greed42/Mini_Drawers_Ultimate/images/0a24cfd5650f65f2fee0652f7383d565_preview_featured.jpg

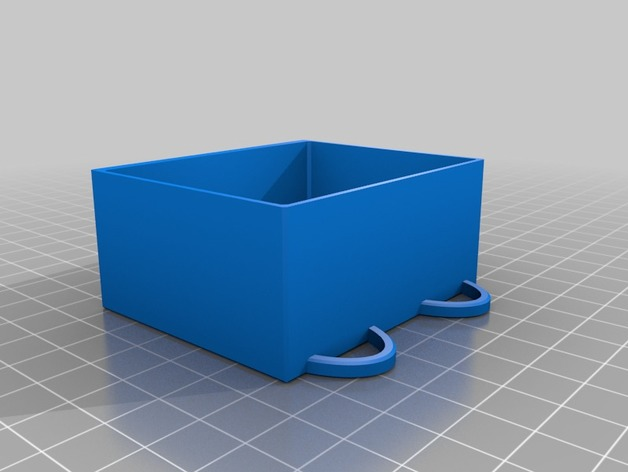
images/0a24cfd5650f65f2fee0652f7383d565_preview_featured.jpg
