greed42/Mini_Drawers_Ultimate/images/0a53dd162b8f72155c7e9e90befe79cb_preview_featured.jpg

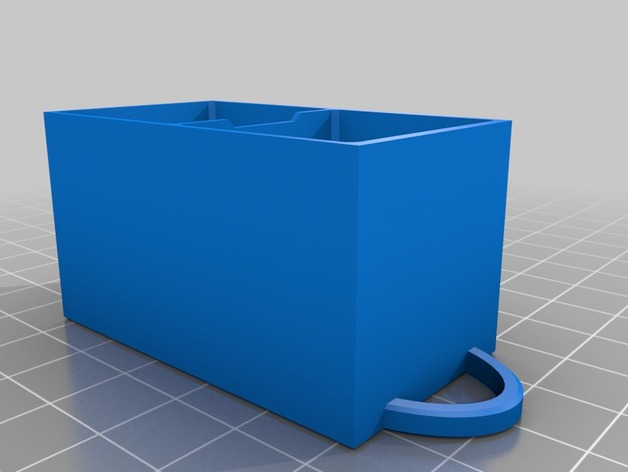
images/0a53dd162b8f72155c7e9e90befe79cb_preview_featured.jpg
