greed42/Mini_Drawers_Ultimate/images/0ca46b2de7a758f1d5402f7cd417421c_preview_featured.jpg

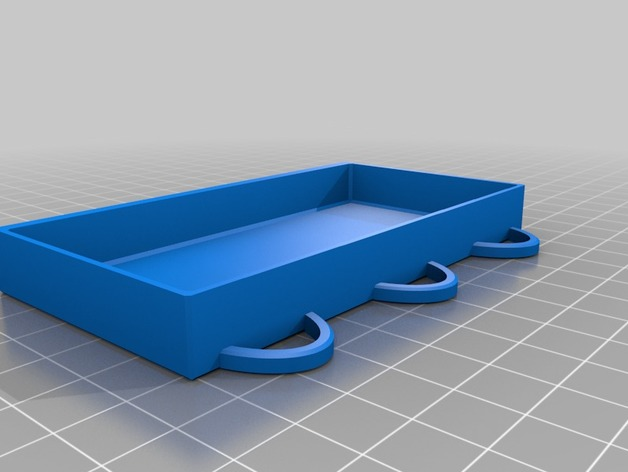
images/0ca46b2de7a758f1d5402f7cd417421c_preview_featured.jpg
