greed42/Mini_Drawers_Ultimate/images/1c9a940551aba49c20e5ade4921b8e68_preview_featured.jpg

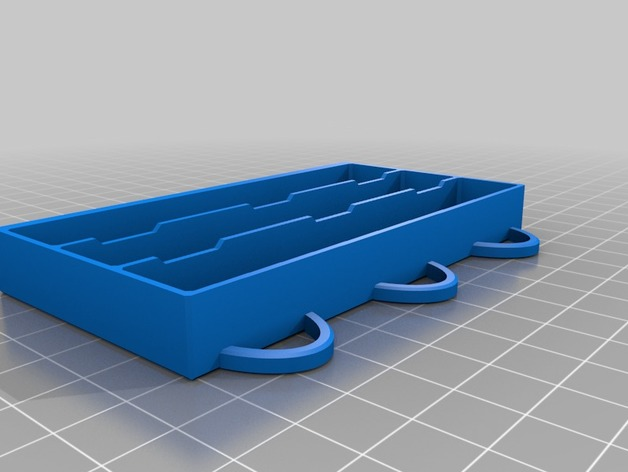
images/1c9a940551aba49c20e5ade4921b8e68_preview_featured.jpg
