greed42/Mini_Drawers_Ultimate/images/2fe49b50781997d6599957611f890632_preview_featured.jpg

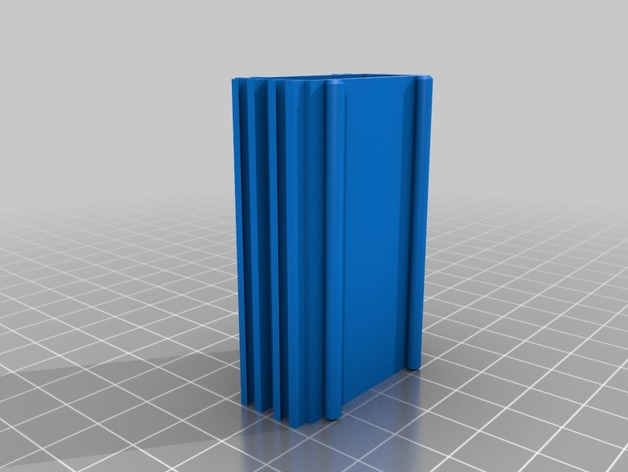
images/2fe49b50781997d6599957611f890632_preview_featured.jpg
