greed42/Mini_Drawers_Ultimate/images/4c2f461d4b738c59763611d66d30dad5_preview_featured.jpg

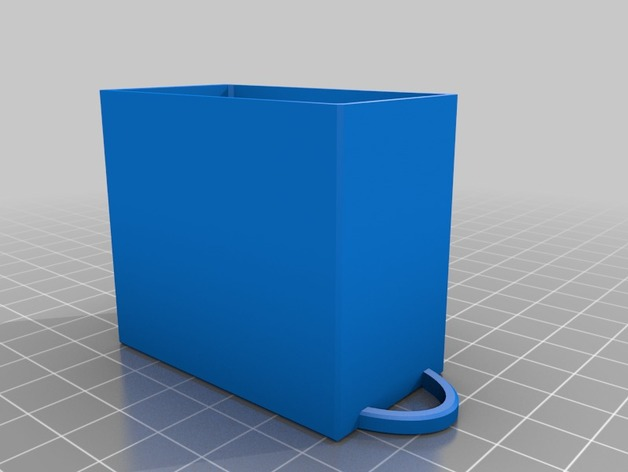
images/4c2f461d4b738c59763611d66d30dad5_preview_featured.jpg
