greed42/Mini_Drawers_Ultimate/images/4ddb12a624d50258dd31a015ba16a962_preview_featured.jpg

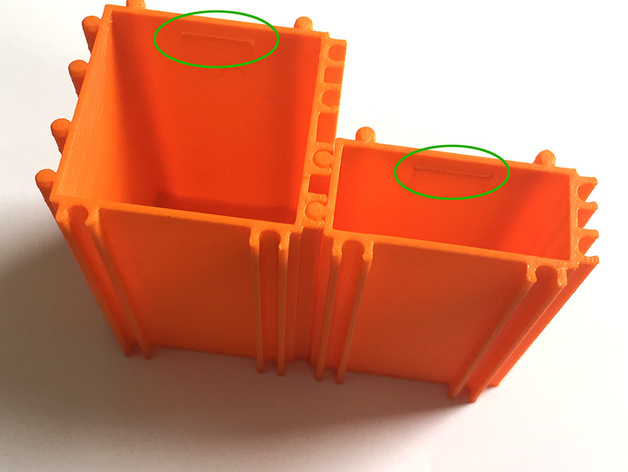
images/4ddb12a624d50258dd31a015ba16a962_preview_featured.jpg
