greed42/Mini_Drawers_Ultimate/images/5e9b697154c2deef4179bea128791556_preview_featured.jpg

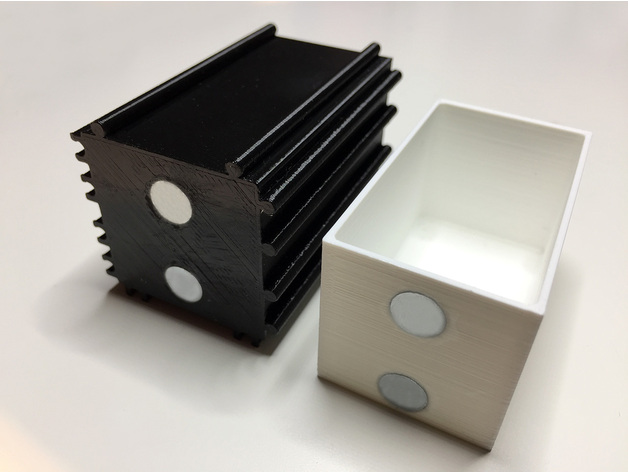
images/5e9b697154c2deef4179bea128791556_preview_featured.jpg
