greed42/Mini_Drawers_Ultimate/images/6dbaf6c8708ecae2bc6790827a99efa1_preview_featured.jpg

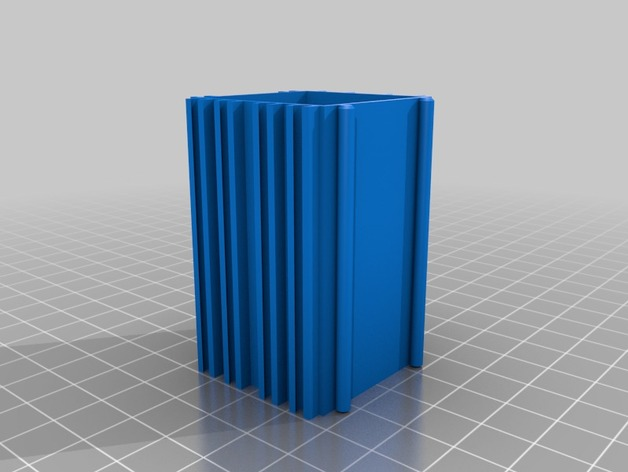
images/6dbaf6c8708ecae2bc6790827a99efa1_preview_featured.jpg
