greed42/Mini_Drawers_Ultimate/images/7b8f287952d526c621f49c0cf82e3b4b_preview_featured.jpg

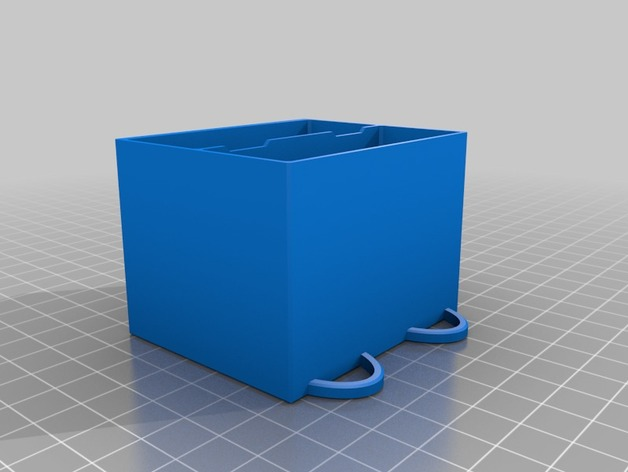
images/7b8f287952d526c621f49c0cf82e3b4b_preview_featured.jpg
