greed42/Mini_Drawers_Ultimate/images/7f0093e2a322c83190b559ce54492e52_preview_featured.jpg

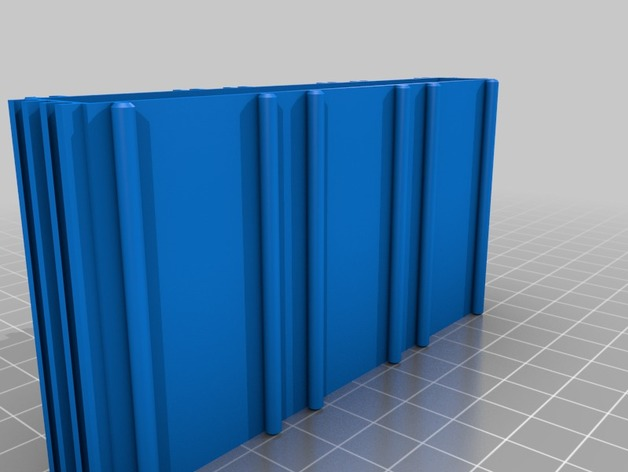
images/7f0093e2a322c83190b559ce54492e52_preview_featured.jpg
