greed42/Mini_Drawers_Ultimate/images/7fe03153f6410948815649d941ac0b7e_preview_featured.jpg

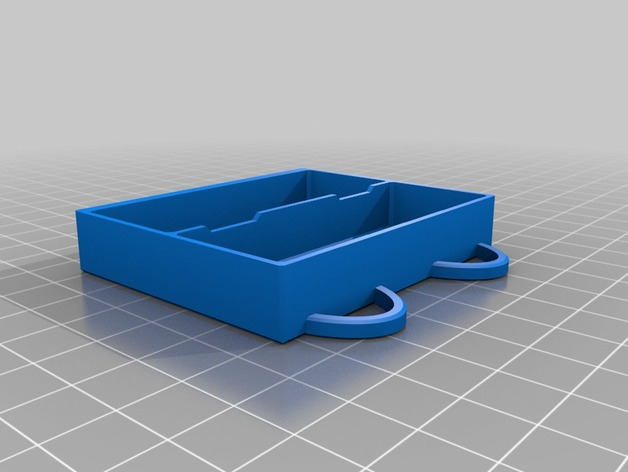
images/7fe03153f6410948815649d941ac0b7e_preview_featured.jpg
