greed42/Mini_Drawers_Ultimate/images/32acb8aaa7054c7361c1b5d2ec2757fa_preview_featured.jpg

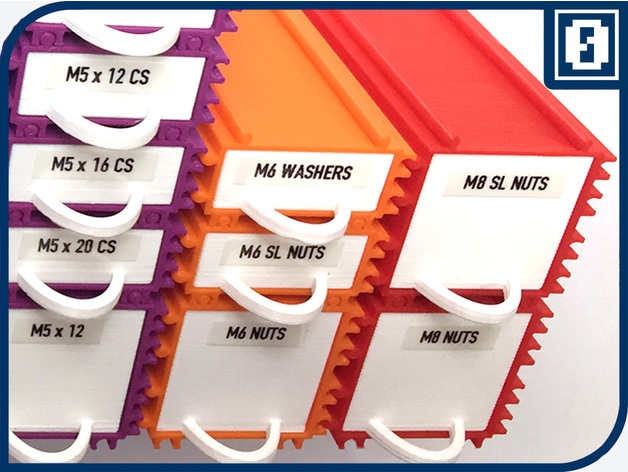
images/32acb8aaa7054c7361c1b5d2ec2757fa_preview_featured.jpg
