greed42/Mini_Drawers_Ultimate/images/32dee0f93447d803b35d06009c72c7d5_preview_featured.jpg

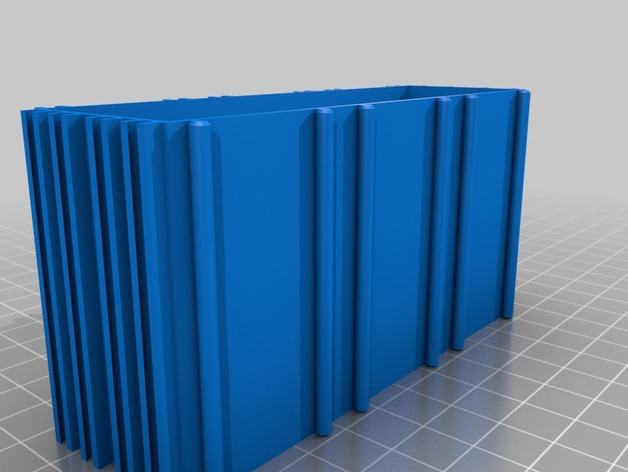
images/32dee0f93447d803b35d06009c72c7d5_preview_featured.jpg
