greed42/Mini_Drawers_Ultimate/images/46a52b9ae08081f0f0b2e6e8d7b132d8_preview_featured.jpg

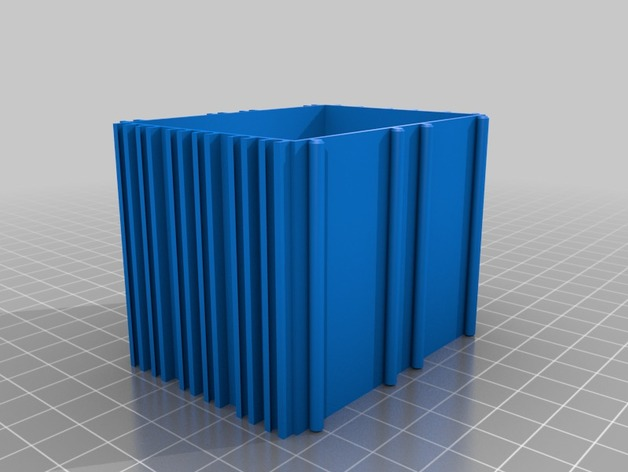
images/46a52b9ae08081f0f0b2e6e8d7b132d8_preview_featured.jpg
