greed42/Mini_Drawers_Ultimate/images/71ca9c4c97bb1e561b7ab4358689eb5e_preview_featured.jpg

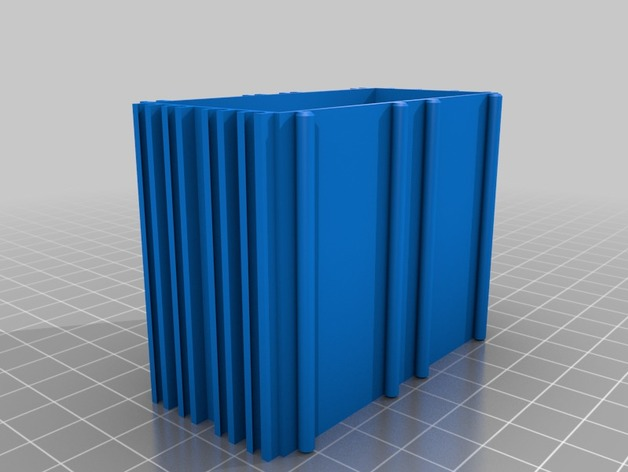
images/71ca9c4c97bb1e561b7ab4358689eb5e_preview_featured.jpg
