greed42/Mini_Drawers_Ultimate/images/408dd901ebeae069e11c7ea489d1516e_preview_featured.jpg

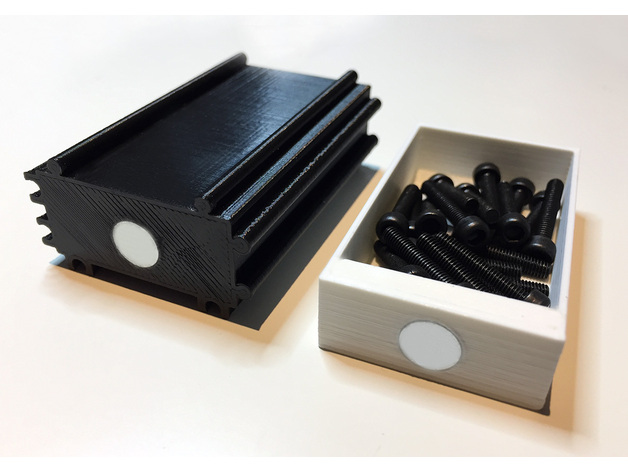
images/408dd901ebeae069e11c7ea489d1516e_preview_featured.jpg
