greed42/Mini_Drawers_Ultimate/images/852ab4ac9241c05d7ac25c2f6cb6ef0e_preview_featured.jpg

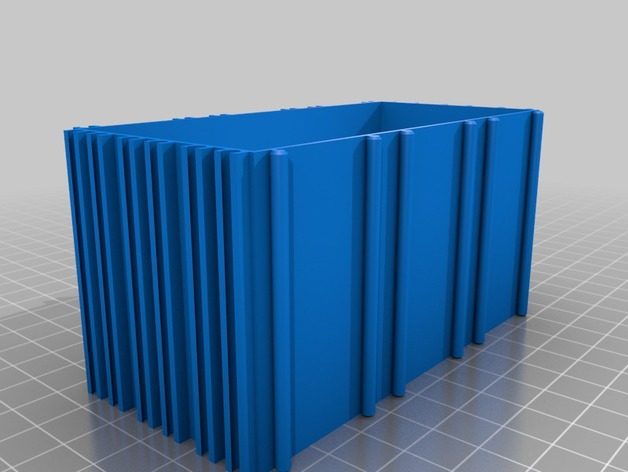
images/852ab4ac9241c05d7ac25c2f6cb6ef0e_preview_featured.jpg
