greed42/Mini_Drawers_Ultimate/images/64127c74380bcbb5a7397c8df0195909_preview_featured.jpg

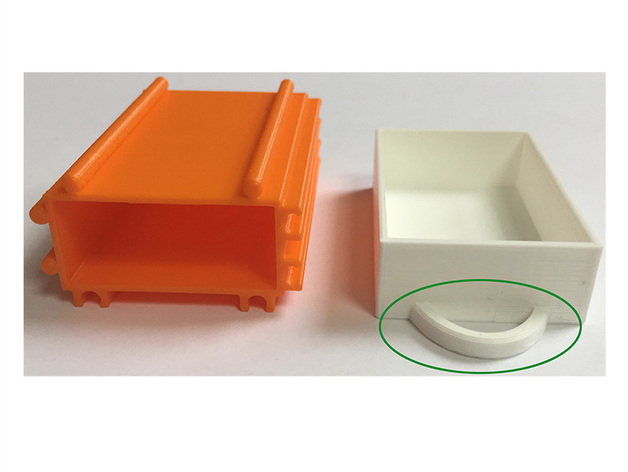
images/64127c74380bcbb5a7397c8df0195909_preview_featured.jpg
