greed42/Mini_Drawers_Ultimate/images/a5263657c8ac7417cfba7f5ac3cf7af2_preview_featured.jpg

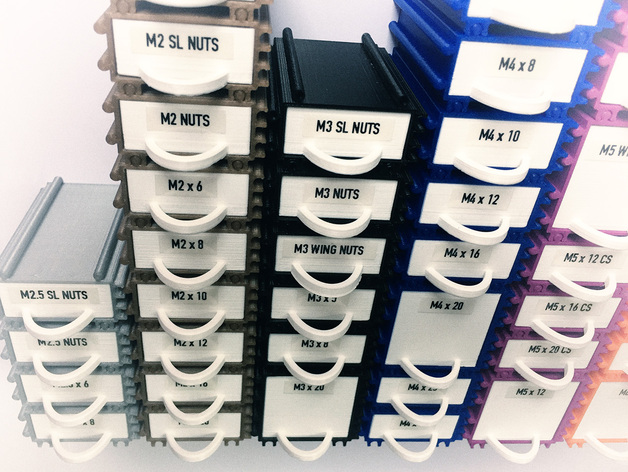
images/a5263657c8ac7417cfba7f5ac3cf7af2_preview_featured.jpg
