greed42/Mini_Drawers_Ultimate/images/c88d1c1aad7d767cea963d23f5f8f326_preview_featured.jpg

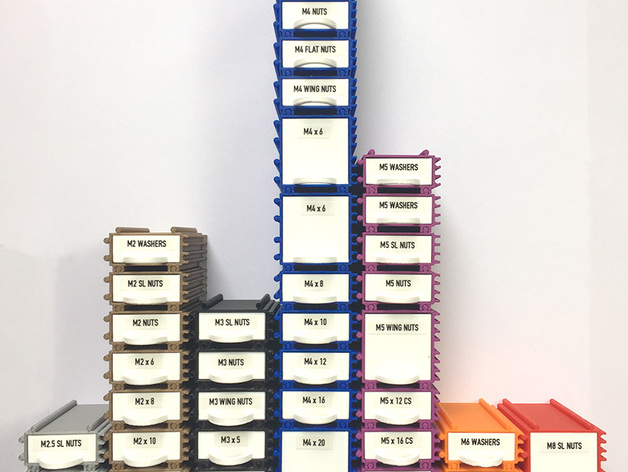
images/c88d1c1aad7d767cea963d23f5f8f326_preview_featured.jpg
