greed42/Mini_Drawers_Ultimate/images/f5fea6e71f09a3ffe9e83b5db6158fe8_preview_featured.JPG

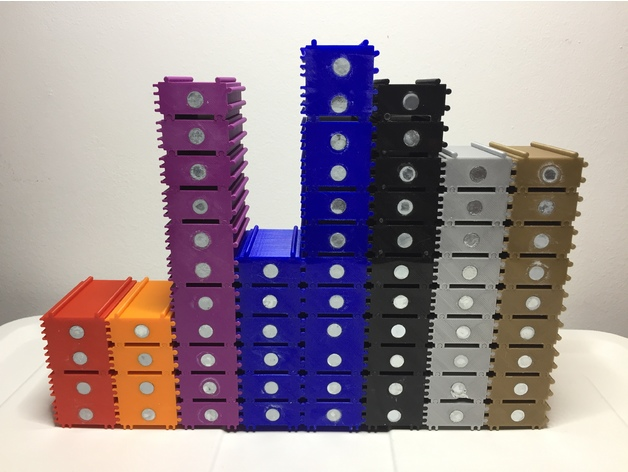
images/f5fea6e71f09a3ffe9e83b5db6158fe8_preview_featured.JPG
