greed42/Mini_Drawers_Ultimate/files/1x1_Drawer_magnet.stl

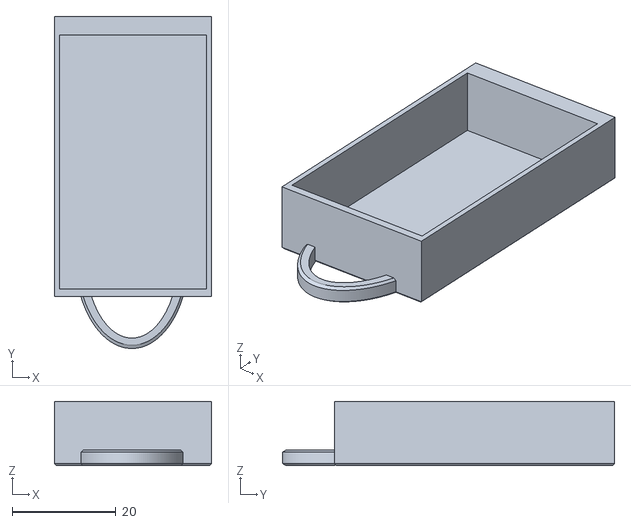
[picture p41: CAD file, 2020-08-03]
files/1x1_Drawer_magnet.stl
30.4 x 64.1 x 12.4
