greed42/Mini_Drawers_Ultimate/files/3x2_House_magnet.stl

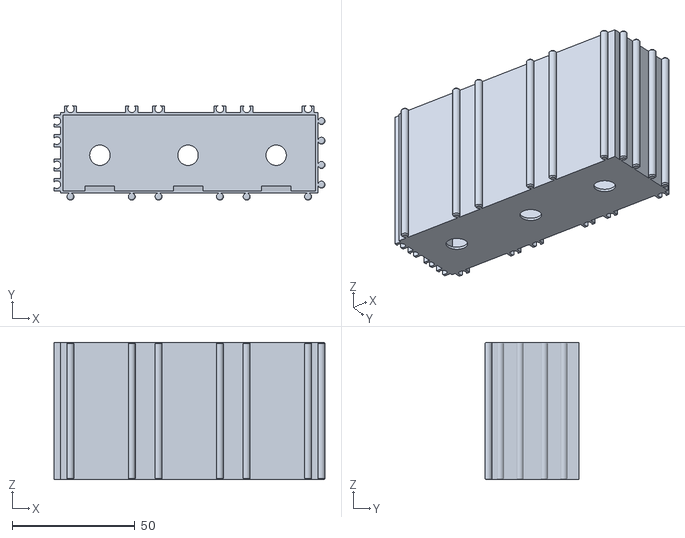
[picture p42: CAD file, 2020-08-03]
files/3x2_House_magnet.stl
110.4 x 38.4 x 56.0
