greed42/Mini_Drawers_Ultimate/files/3x1_Drawer_-_three_slots_magnet.stl

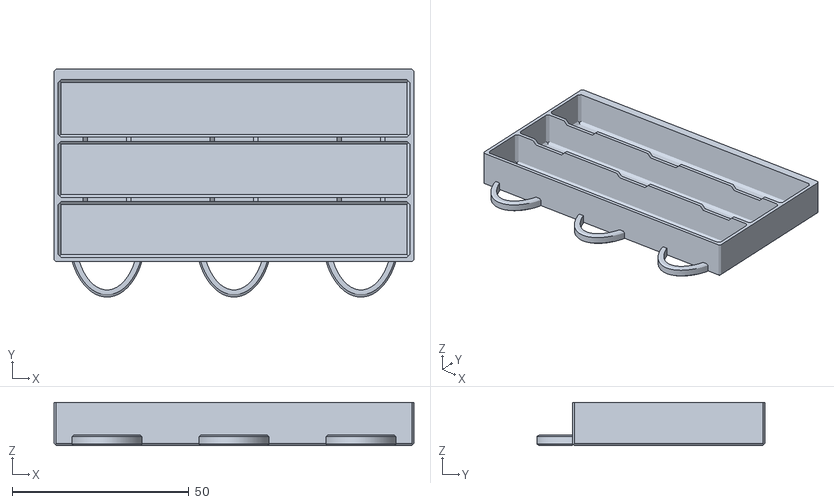
[picture p45: CAD file, 2020-08-03]
files/3x1_Drawer_-_three_slots_magnet.stl
101.8 x 64.5 x 12.2
