greed42/Mini_Drawers_Ultimate/files/1x3_House_magnet.stl

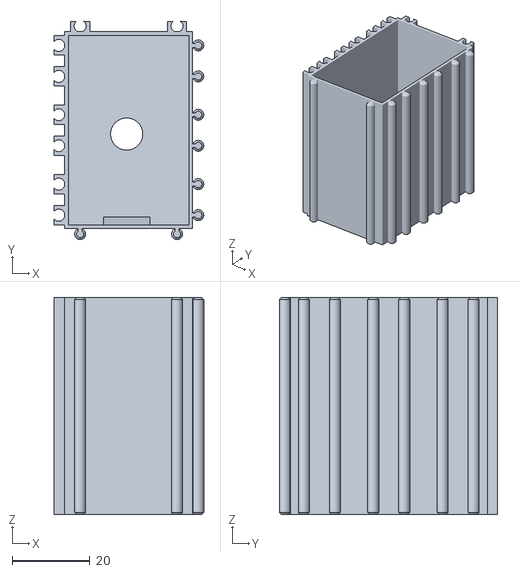
[picture p46: CAD file, 2020-08-03]
files/1x3_House_magnet.stl
38.6 x 56.3 x 56.0
