greed42/Mini_Drawers_Ultimate/files/2x2_House_magnet.stl

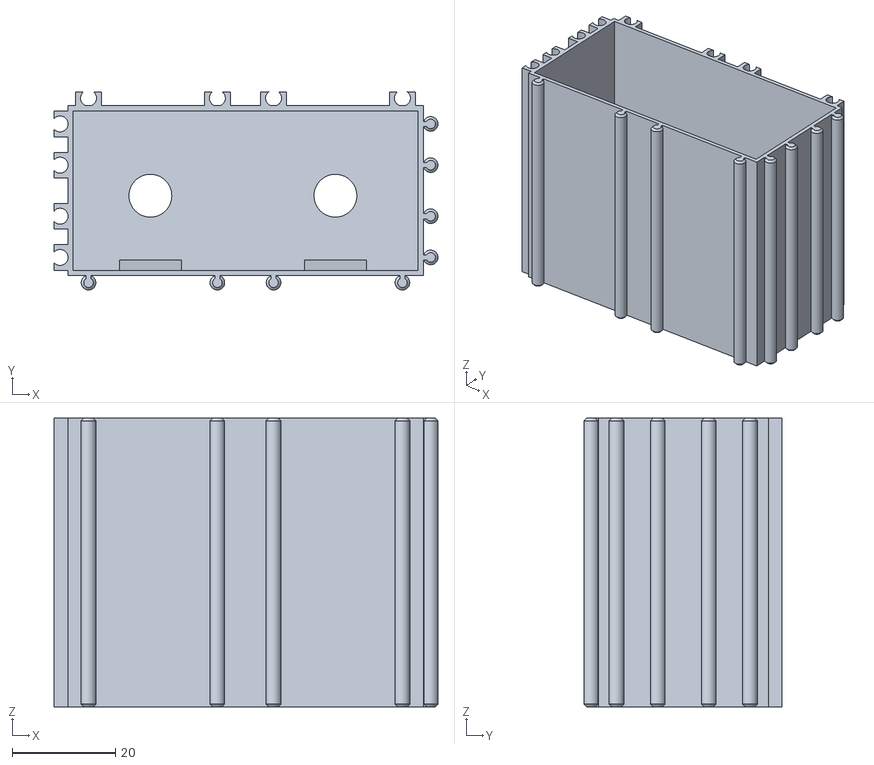
[picture p48: CAD file, 2020-08-03]
files/2x2_House_magnet.stl
74.5 x 38.4 x 56.0
