greed42/Mini_Drawers_Ultimate/files/2x1_Drawer_-_three_slots_magnet.stl

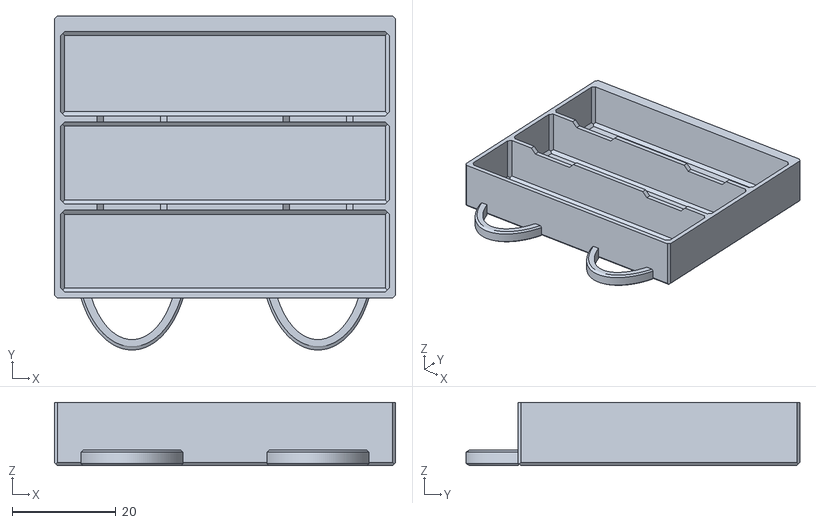
[picture p49: CAD file, 2020-08-03]
files/2x1_Drawer_-_three_slots_magnet.stl
65.9 x 64.5 x 12.2
