greed42/Mini_Drawers_Ultimate/files/3x3_Drawer_-_two_slots_magnet.stl

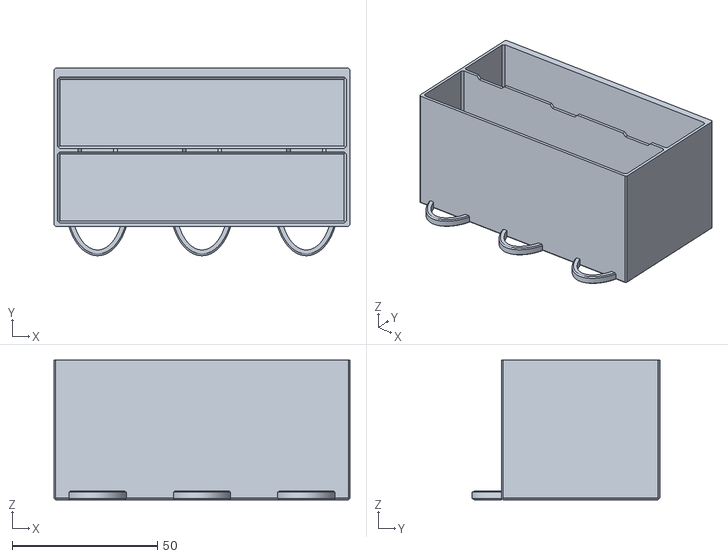
[picture p51: CAD file, 2020-08-03]
files/3x3_Drawer_-_two_slots_magnet.stl
101.8 x 64.5 x 48.0
