greed42/Mini_Drawers_Ultimate/files/3x1_House.stl

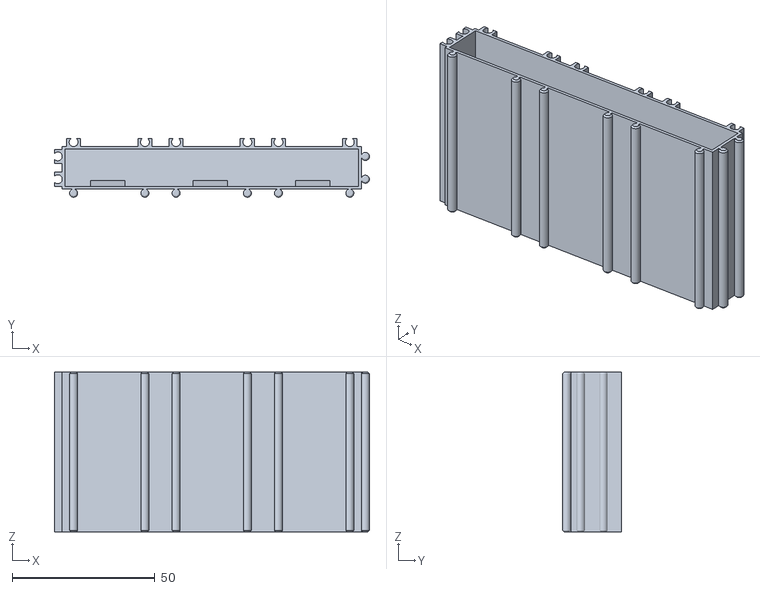
[picture p52: CAD file, 2020-08-03]
files/3x1_House.stl
110.4 x 20.5 x 56.0
