greed42/Mini_Drawers_Ultimate/files/1x1_Drawer_-_two_slots.stl

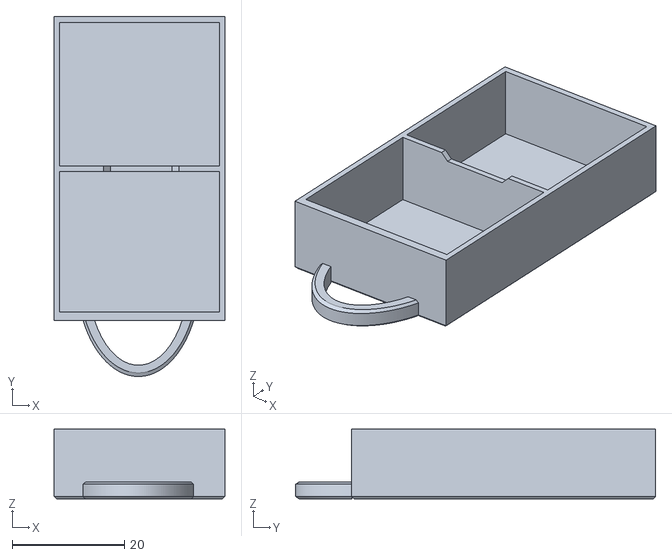
[picture p53: CAD file, 2020-08-03]
files/1x1_Drawer_-_two_slots.stl
30.4 x 64.1 x 12.4
