greed42/Mini_Drawers_Ultimate/files/1x2_House.stl

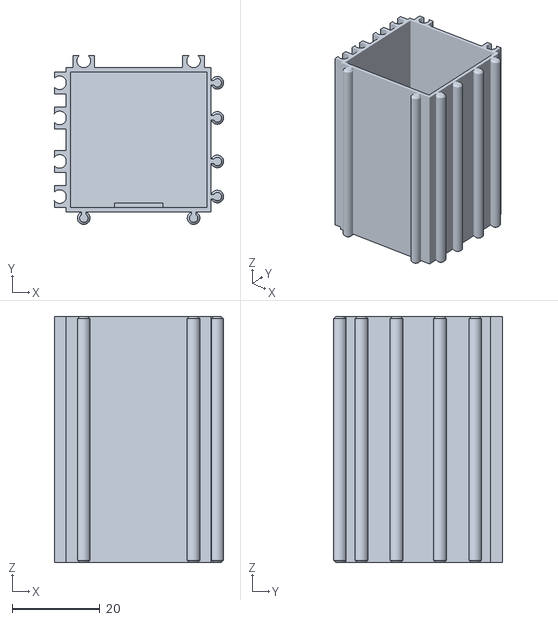
[picture p55: CAD file, 2020-08-03]
files/1x2_House.stl
38.6 x 38.4 x 56.0
