greed42/Mini_Drawers_Ultimate/files/1x2_House_magnet.stl

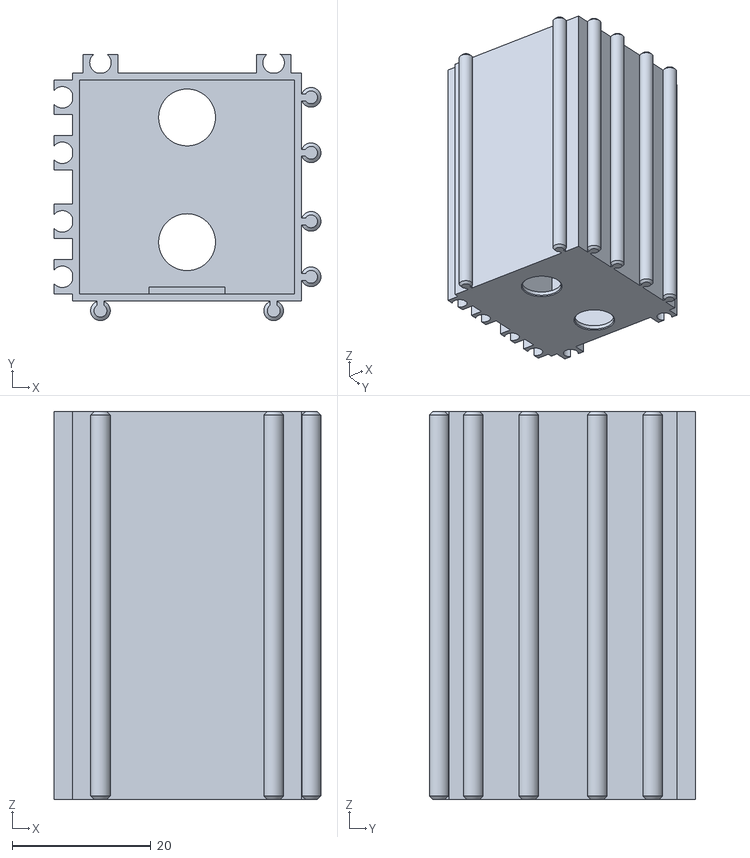
[picture p59: CAD file, 2020-08-03]
files/1x2_House_magnet.stl
38.5 x 38.4 x 56.0
