greed42/Mini_Drawers_Ultimate/files/2x1_Drawer_magnet.stl

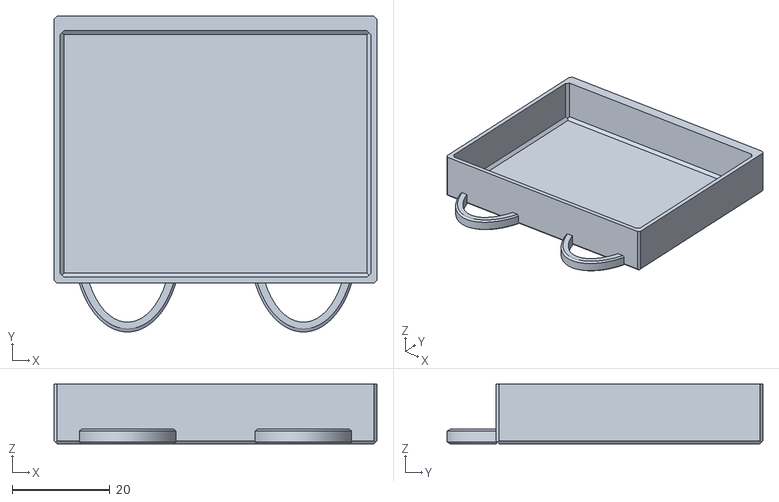
[picture p60: CAD file, 2020-08-03]
files/2x1_Drawer_magnet.stl
65.9 x 64.5 x 12.2
