greed42/Mini_Drawers_Ultimate/files/1x3_Drawer_-_two_slots_magnet.stl

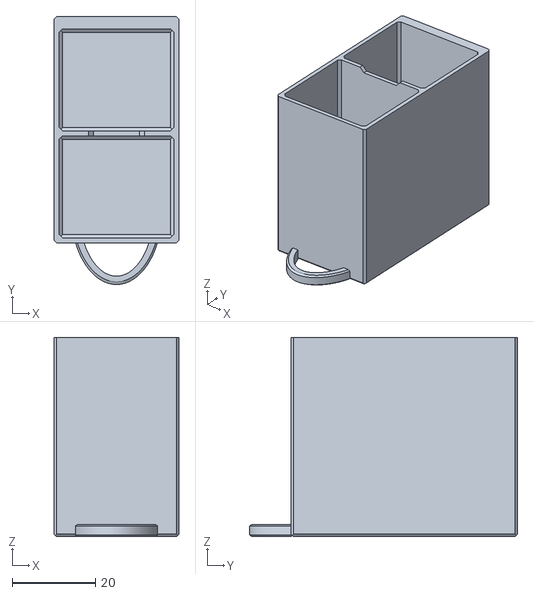
[picture p61: CAD file, 2020-08-03]
files/1x3_Drawer_-_two_slots_magnet.stl
30.0 x 64.5 x 48.0
