greed42/Mini_Drawers_Ultimate/files/1x1_House_magnet.stl

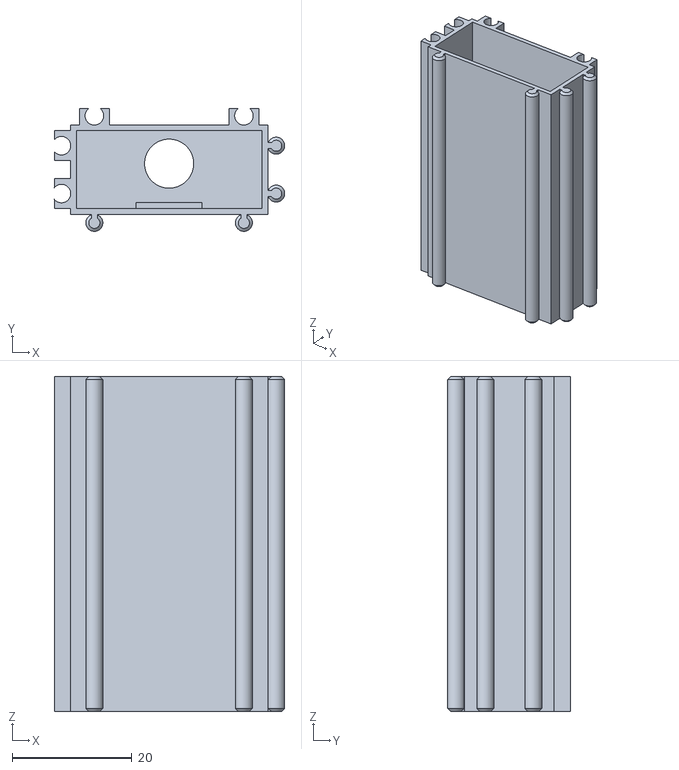
[picture p62: CAD file, 2020-08-03]
files/1x1_House_magnet.stl
38.5 x 20.5 x 56.0
