greed42/Mini_Drawers_Ultimate/files/3x1_House_magnet.stl

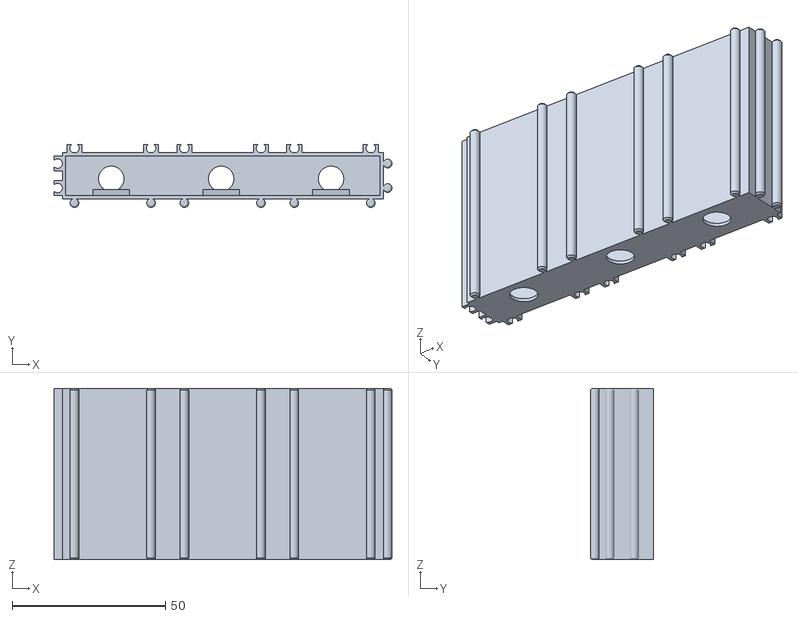
[picture p63: CAD file, 2020-08-03]
files/3x1_House_magnet.stl
110.4 x 20.5 x 56.0
