greed42/Mini_Drawers_Ultimate/files/1x2_Drawer.stl

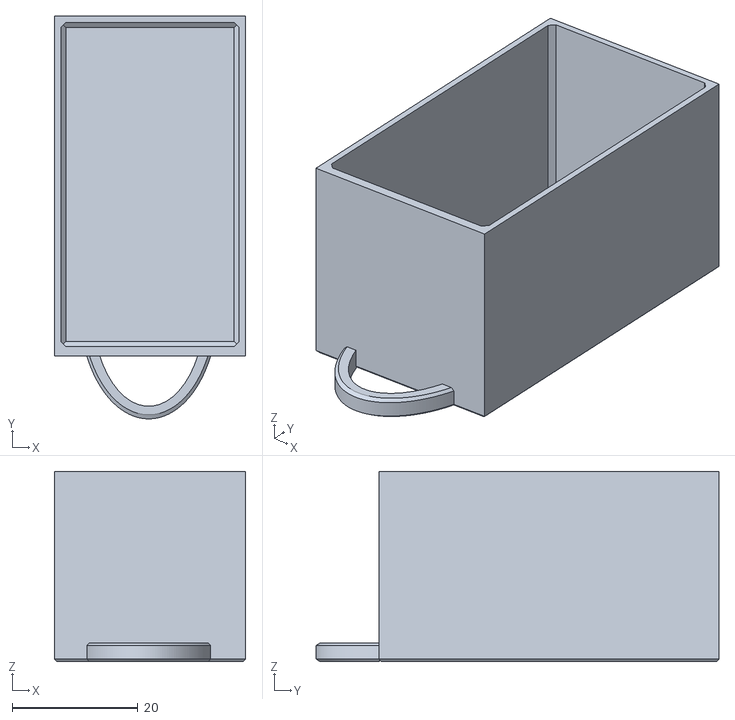
[picture p65: CAD file, 2020-08-03]
files/1x2_Drawer.stl
30.4 x 64.1 x 30.3
