greed42/Mini_Drawers_Ultimate/files/3x3_Drawer_-_three_slots.stl

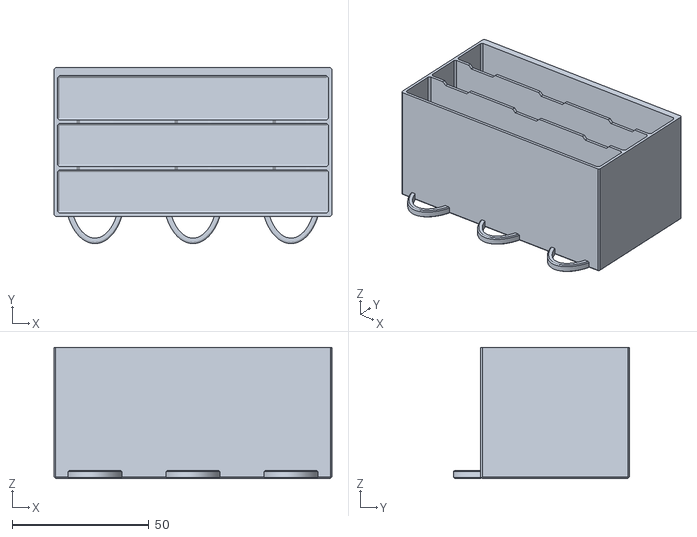
[picture p66: CAD file, 2020-08-03]
files/3x3_Drawer_-_three_slots.stl
101.8 x 64.5 x 48.0
