greed42/Mini_Drawers_Ultimate/files/2x3_House_magnet.stl

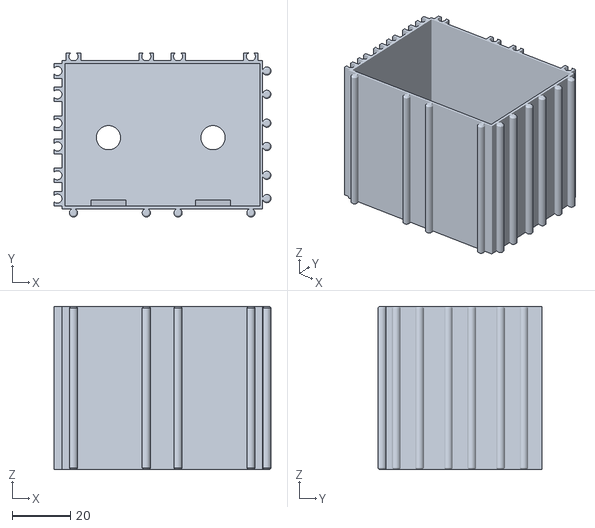
[picture p67: CAD file, 2020-08-03]
files/2x3_House_magnet.stl
74.5 x 56.3 x 56.0
