greed42/Mini_Drawers_Ultimate/files/2x1_Drawer.stl

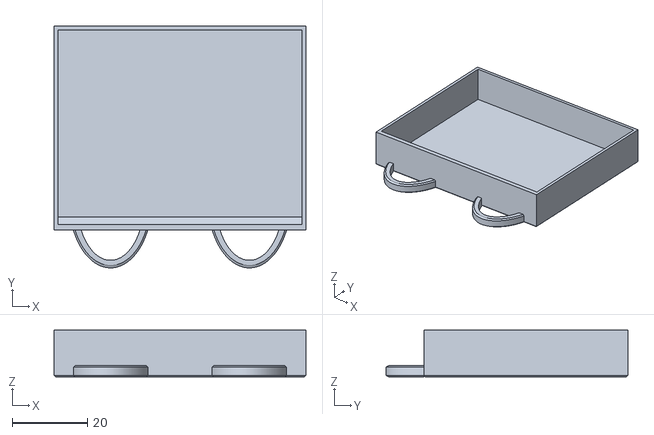
[picture p68: CAD file, 2020-08-03]
files/2x1_Drawer.stl
66.8 x 64.1 x 12.4
