greed42/Mini_Drawers_Ultimate/files/SCAD files/MD House 1x1 (magnet).scad

include <Chamfer.scad>;
// edit here
runnersDiameter = 2.85;
squareMagnet = false;
magnetSize = 8; //mm
// do not edit below this line

$fn = 50;
height = 56; // in millimeters

house();

module house()
{
  //
  // case
  difference()
  {
    cube([33,15,height]);
    translate([1,1,1]) cube([31,13,height]); // hollow out drawer
    if ( squareMagnet ) {
      translate([16.5-magnetSize/2,8.5-magnetSize/2,-0.2]) cube([magnetSize,magnetSize,1.5]); // magnet hole
    } else {
      translate([16.5,8.5,-0.2]) cylinder(h=1.3,r=(magnetSize/2)+.1,$fn=100); // magnet hole
      translate([16.5,8.5,-0.2]) cylinder(.4,(magnetSize/2)+.4,(magnetSize/2)+.1); // chamfer on bottom-side of magnet hole
    }
  }

  //
  // runners
  radius = runnersDiameter/2;
  // bottom
  translate([ 4,  -1.4, 0]) chamferCylinder(height,radius,radius,.5);
  translate([ 3.5,-1.5, 0]) cube([1,1.6,height]);
  translate([29,  -1.4, 0]) chamferCylinder(height,radius,radius,.5);
  translate([28.5,-1.5, 0]) cube([1,1.6,height]);
  // right
  translate([34.4, 3.5,0]) chamferCylinder(height,radius,radius,.5);
  translate([32.9, 3,  0]) cube([1.6,1,height]);
  translate([34.4,11.5,0]) chamferCylinder(height,radius,radius,.5);
  translate([32.9,11,  0]) cube([1.6,1,height]);

  //
  // slots
  difference()
  {
    union()
    {
      translate([ 1.5,  14.9, 0]) cube([5,2.8,height]);
      translate([26.5,  14.9, 0]) cube([5,2.8,height]);
      translate([-2.7,   1,   0]) cube([2.8,5,height]);
      translate([-2.7,   9,   0]) cube([2.8,5,height]);
    }
    translate([ 4,  16.5, -0.1]) cylinder(d=3.1,h=height+02);
    translate([29,  16.5, -0.1]) cylinder(d=3.1,h=height+02);
    translate([-1.5, 3.5, -0.1]) cylinder(d=3.1,h=height+02);
    translate([-1.5,11.5, -0.1]) cylinder(d=3.1,h=height+02);
  }
  
  //
  // stopper
  translate([11,2,height-2]) rotate( [0,180,180] ) prism(l=11,w=1,h=10);
}

module prism(l, w, h)
{
  polyhedron(
    points=[[0,0,0], [l,0,0], [l,w,0], [0,w,0], [0,w,h], [l,w,h]],
    faces=[[0,1,2,3],[5,4,3,2],[0,4,5,1],[0,3,4],[5,2,1]]
  );     
}
